bear454/keyboard/print/keycaps-caps_1.5u-legend.stl

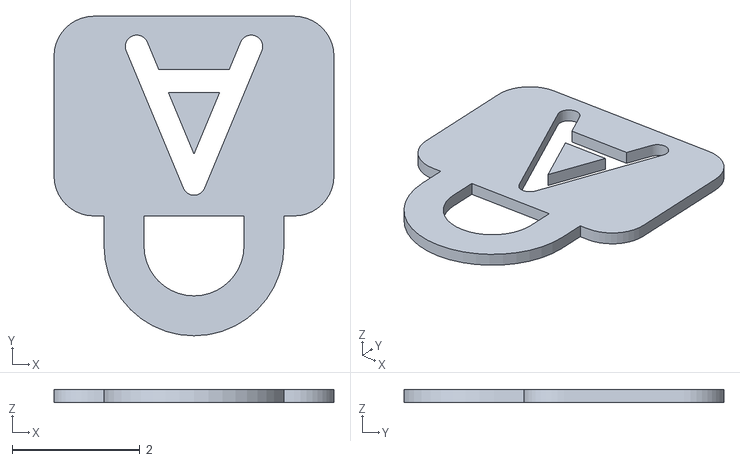
[picture p16: CAD file, 2022-10-12]
print/keycaps-caps_1.5u-legend.stl
4.38 x 5.00 x 0.2
