bear454/keyboard/print/keycaps-pgdn-legend.stl

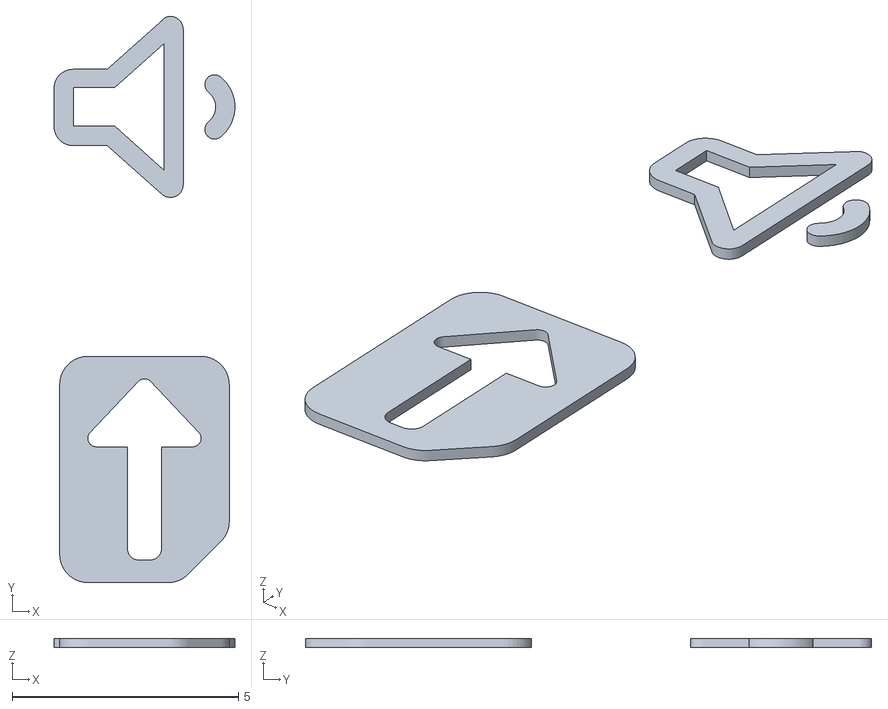
[picture p17: CAD file, 2022-10-12]
print/keycaps-pgdn-legend.stl
4.00 x 12.5 x 0.2
