bear454/keyboard/print/keycaps-shift_2u-legend.stl

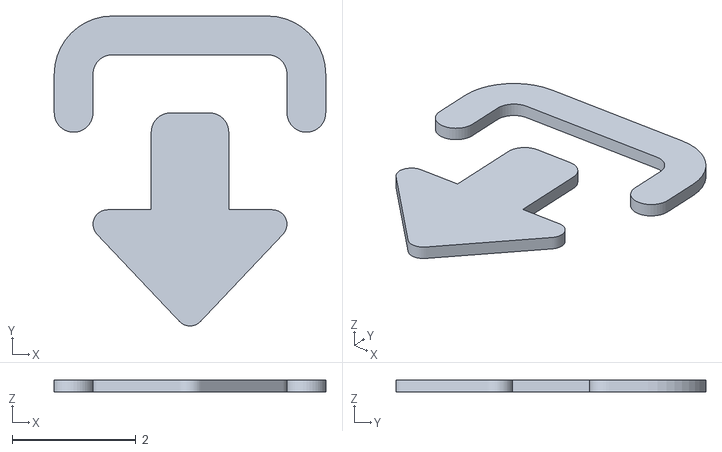
[picture p18: CAD file, 2022-10-12]
print/keycaps-shift_2u-legend.stl
4.38 x 5.00 x 0.2
