bear454/keyboard/print/keycaps-ctrl_1.5u-legend.stl

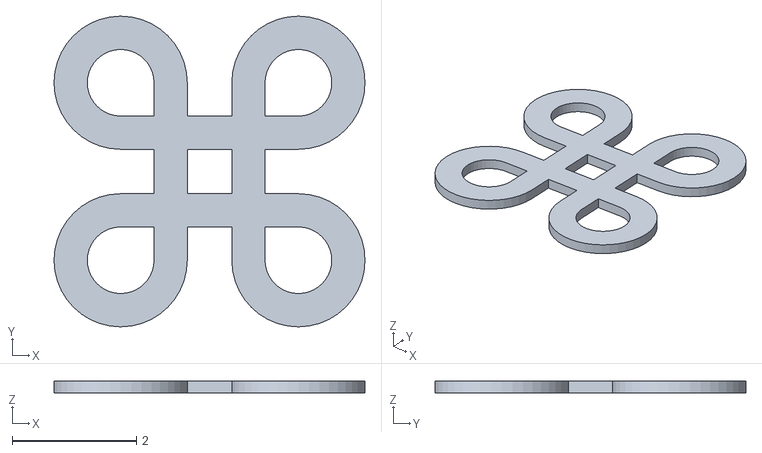
[picture p19: CAD file, 2022-10-12]
print/keycaps-ctrl_1.5u-legend.stl
5.00 x 5.00 x 0.2
