bear454/keyboard/print/keycaps-window-legend.stl

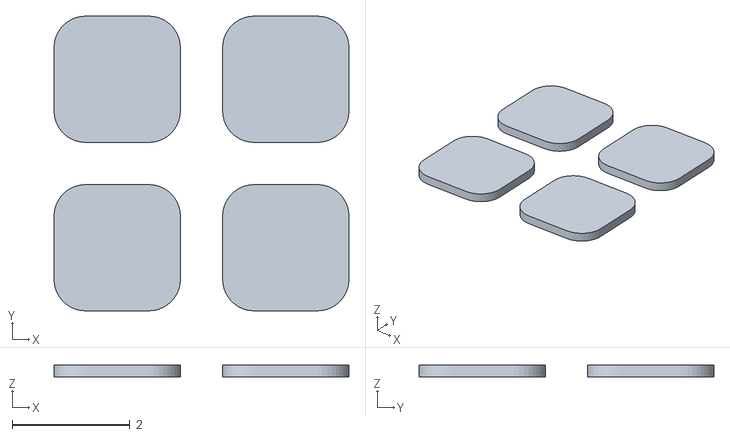
[picture p20: CAD file, 2022-10-12]
print/keycaps-window-legend.stl
5.00 x 5.00 x 0.2
