bear454/keyboard/print/keycaps-del-legend.stl

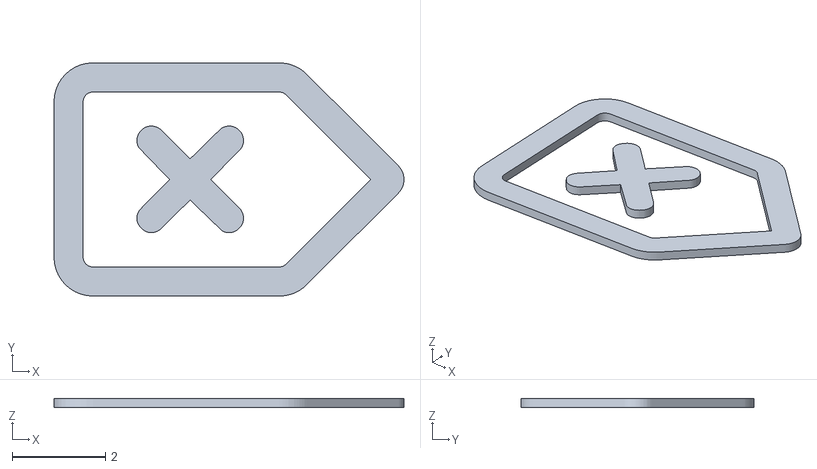
[picture p21: CAD file, 2022-10-12]
print/keycaps-del-legend.stl
7.51 x 5.00 x 0.2
