bear454/keyboard/print/keycaps-pgup-legend.stl

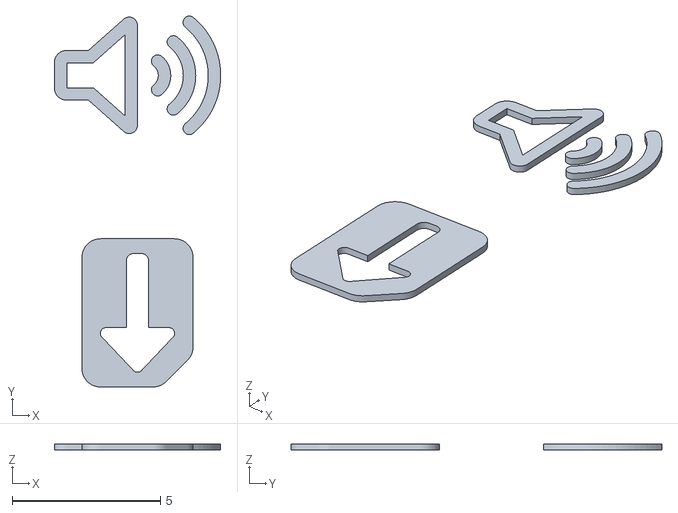
[picture p22: CAD file, 2022-10-12]
print/keycaps-pgup-legend.stl
5.61 x 12.5 x 0.2
