bear454/keyboard/print/keycaps-window-face.stl

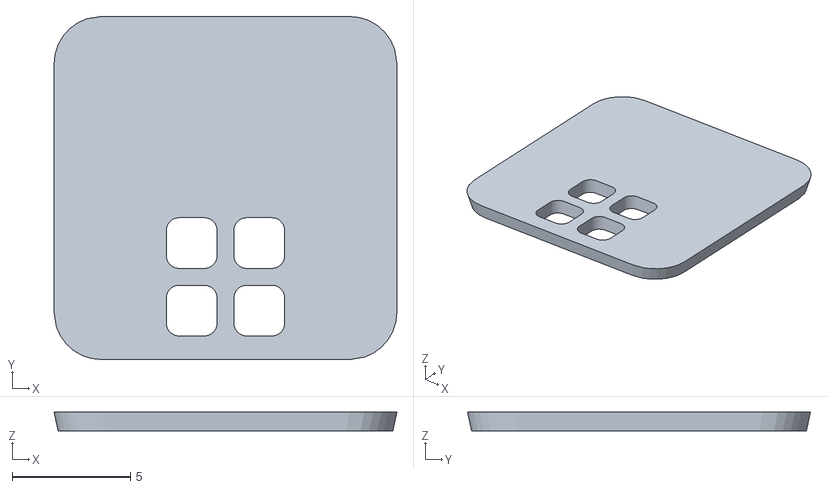
[picture p23: CAD file, 2022-10-12]
print/keycaps-window-face.stl
14.5 x 14.5 x 0.798
