bear454/keyboard/print/keycaps-shift_2u-body.stl

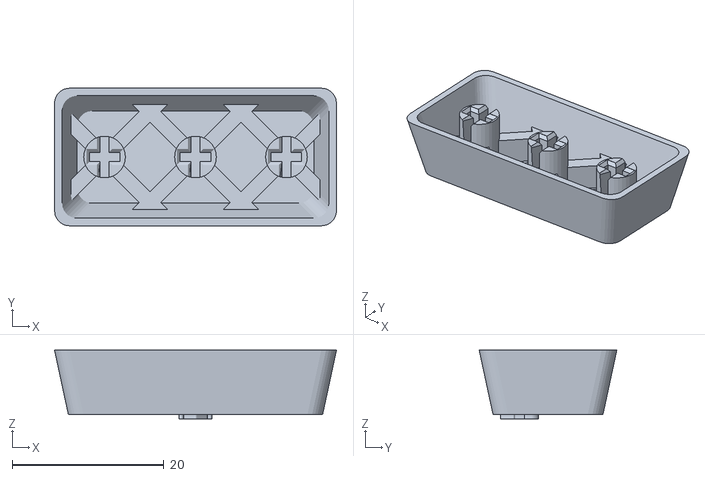
[picture p24: CAD file, 2022-10-12]
print/keycaps-shift_2u-body.stl
37.2 x 18.2 x 9.10
