bear454/keyboard/print/keycaps-enter_1.5u-legend.stl

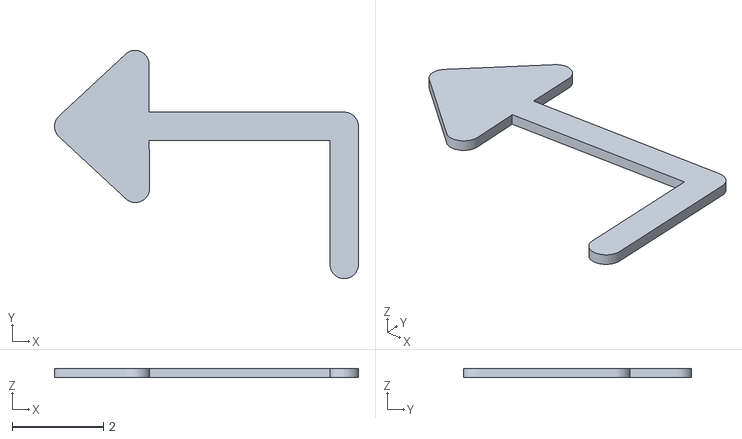
[picture p25: CAD file, 2022-10-12]
print/keycaps-enter_1.5u-legend.stl
6.65 x 5.00 x 0.2
