bear454/keyboard/print/keycaps-shift_2u-face.stl

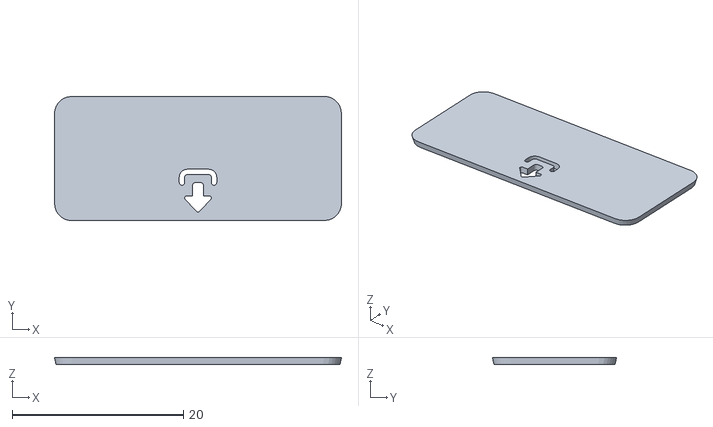
[picture p26: CAD file, 2022-10-12]
print/keycaps-shift_2u-face.stl
33.6 x 14.5 x 0.798
